capotosto/PS_Monitor/hardware/Isolated Multi-Rail Power Supply Monitor Arduino Shield Board/Outputs/STEP/CGS-PSM-12_Rev-A_bottom.png

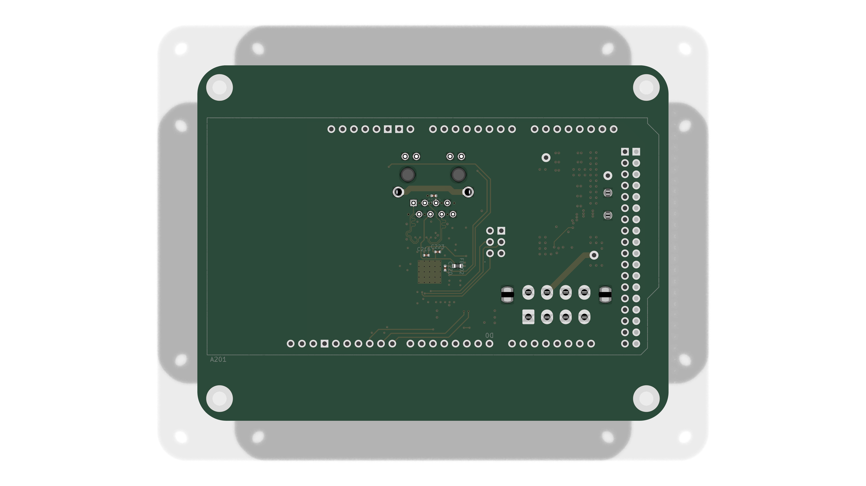
hardware/Isolated Multi-Rail Power Supply Monitor Arduino Shield Board/Outputs/STEP/CGS-PSM-12_Rev-A_bottom.png
