capotosto/PS_Monitor/hardware/Isolated Multi-Rail Power Supply Monitor Sensor Board/Outputs/STEP/CGS-PSM-02_Rev-A_bottom.png

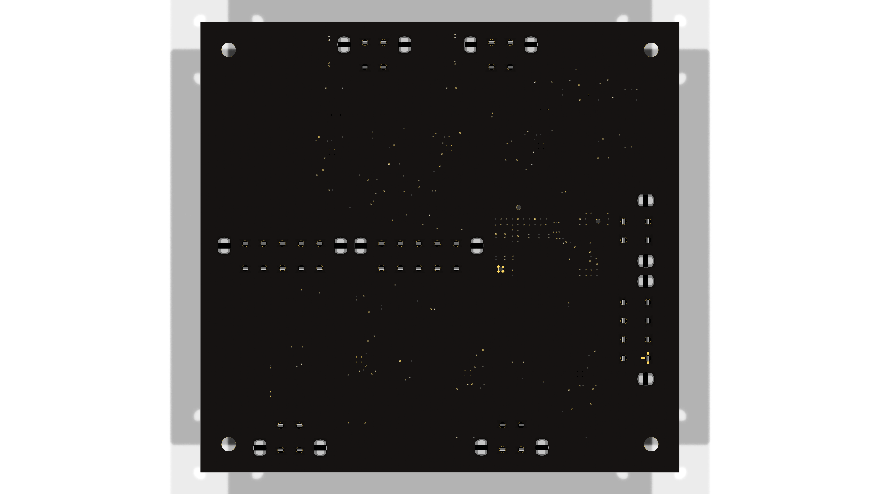
hardware/Isolated Multi-Rail Power Supply Monitor Sensor Board/Outputs/STEP/CGS-PSM-02_Rev-A_bottom.png
