capotosto/PS_Monitor/documentation/Pictures/Phoebus-SS-N5V-Test-3k3Load.png

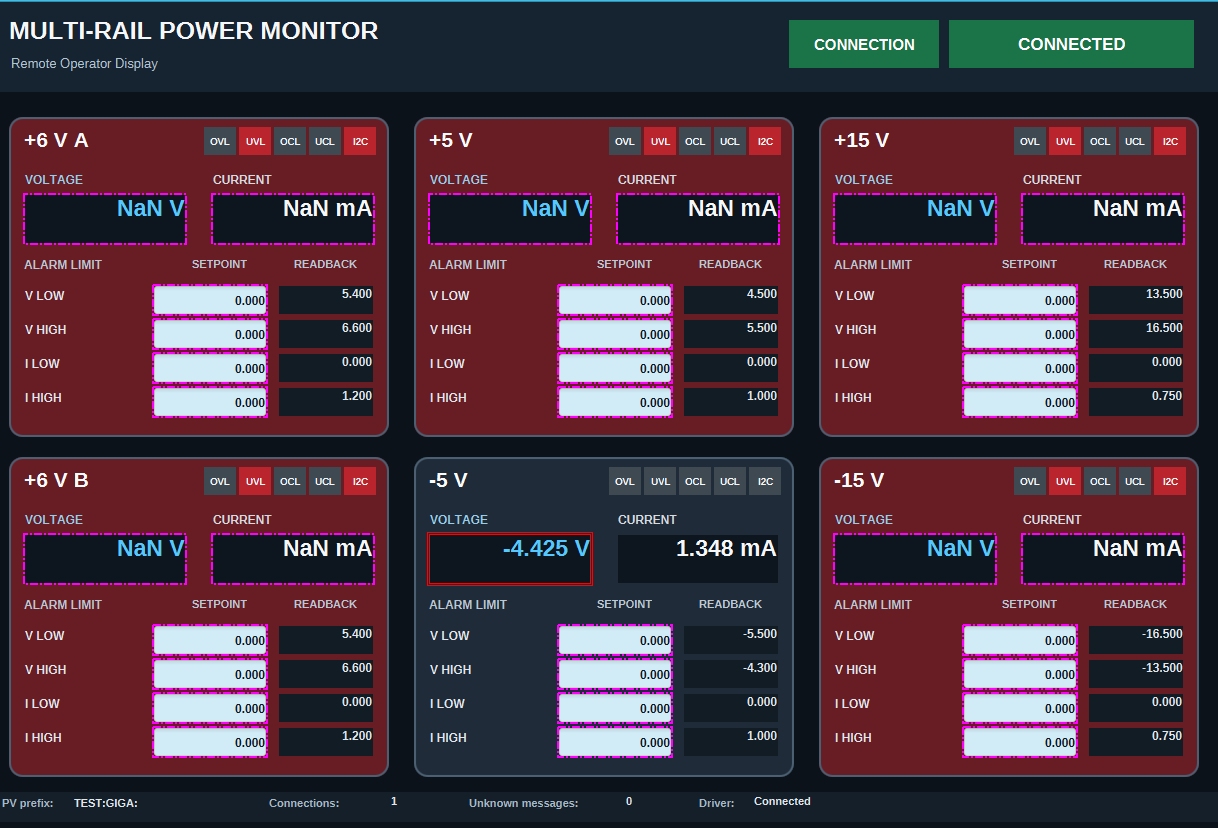
documentation/Pictures/Phoebus-SS-N5V-Test-3k3Load.png
