capotosto/PS_Monitor/documentation/Pictures/Phoebus-SS-N5V-Test-NoLoad-I2C-Fault.png

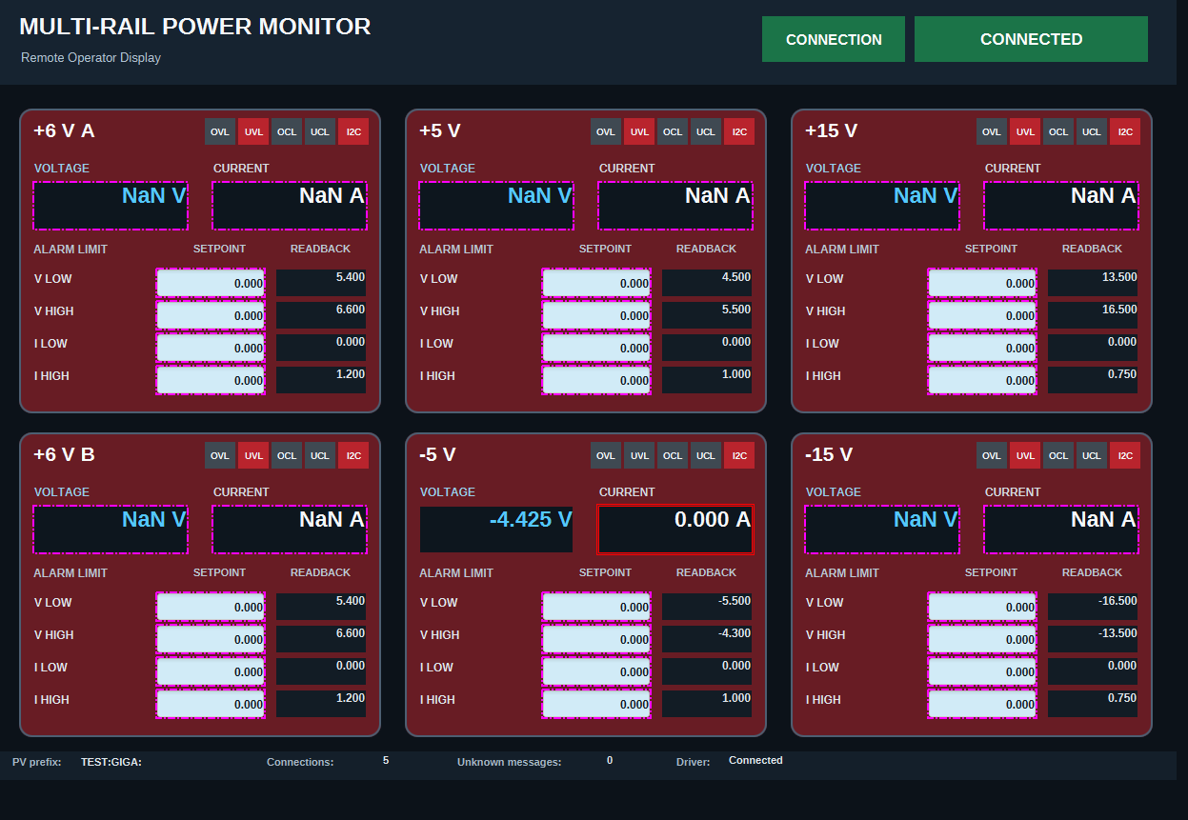
documentation/Pictures/Phoebus-SS-N5V-Test-NoLoad-I2C-Fault.png
