capotosto/PS_Monitor/documentation/Pictures/Phoebus-SS-N5V-Test-NoLoad.png

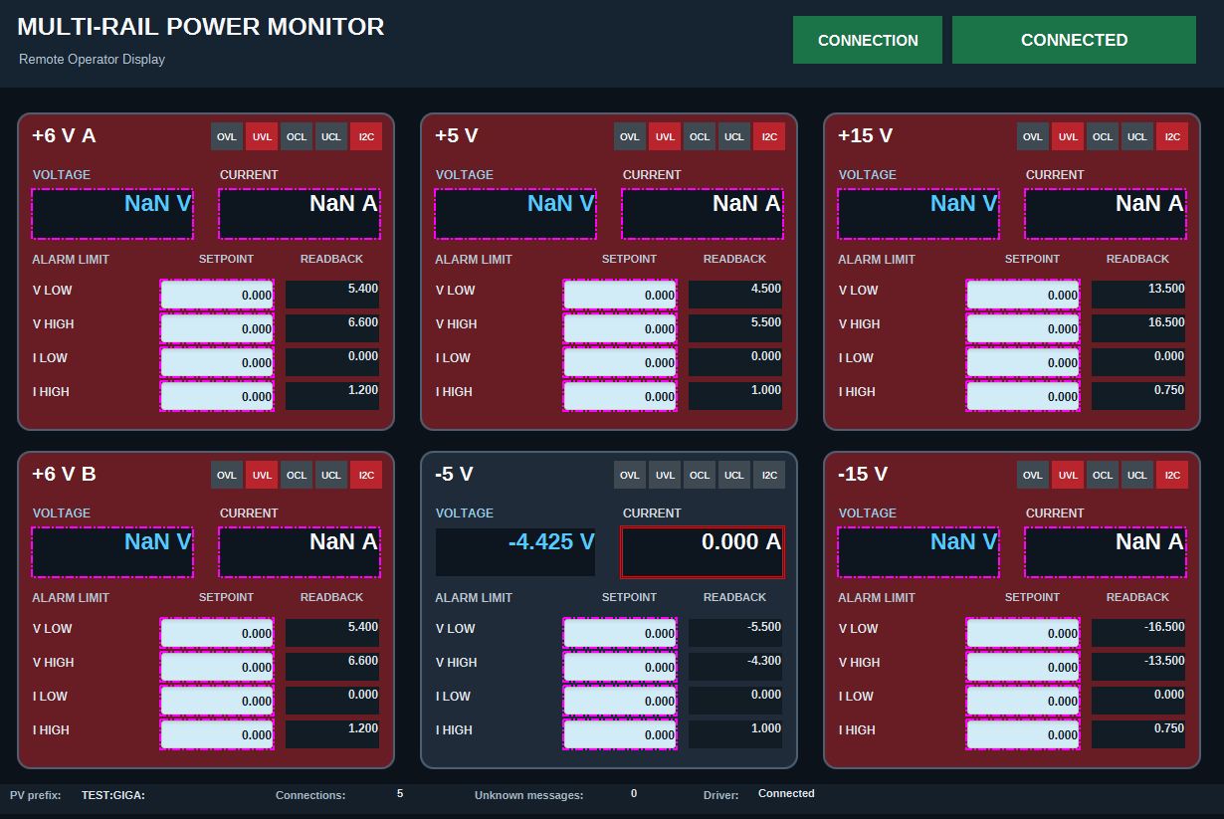
documentation/Pictures/Phoebus-SS-N5V-Test-NoLoad.png
