capotosto/PS_Monitor/documentation/Pictures/SimulationResults.png

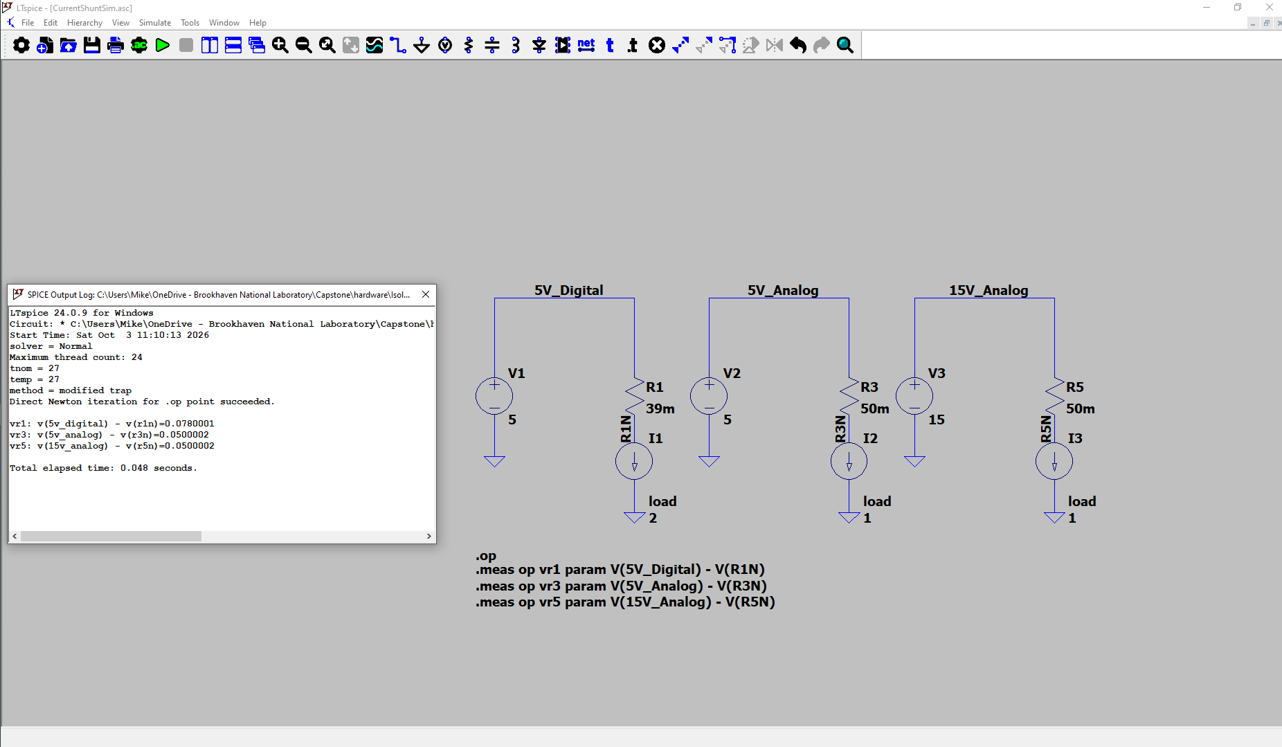
documentation/Pictures/SimulationResults.png
