capotosto/PS_Monitor/hardware/Isolated Multi-Rail Power Supply Monitor Sensor Board/Simulations/CurrentShuntSim.asc

I1: current; 2; load
I2: current; 1; load
I3: current; 1; load
R1: res; 39m; tol=0
R3: res; 50m; tol=0
R5: res; 50m; tol=0
V1: voltage; 5
V2: voltage; 5
V3: voltage; 15
Named nets: 0, 5V_Digital, 5V_Analog, 15V_Analog, R1N, R3N, R5N
.op
.meas op vr1 param V(5V_Digital) - V(R1N)
.meas op vr3 param V(5V_Analog) - V(R3N)
.meas op vr5 param V(15V_Analog) - V(R5N)
