capotosto/PS_Monitor/hardware/Isolated Multi-Rail Power Supply Monitor Arduino Shield Board/Isolated Multi-Rail Power Supply Monitor Arduino Shield Board.kicad_sch

## KiCad design hardware/Isolated Multi-Rail Power Supply Monitor Arduino Shield Board/Isolated Multi-Rail Power Supply Monitor Arduino Shield Board.kicad_sch (2026-09-21)

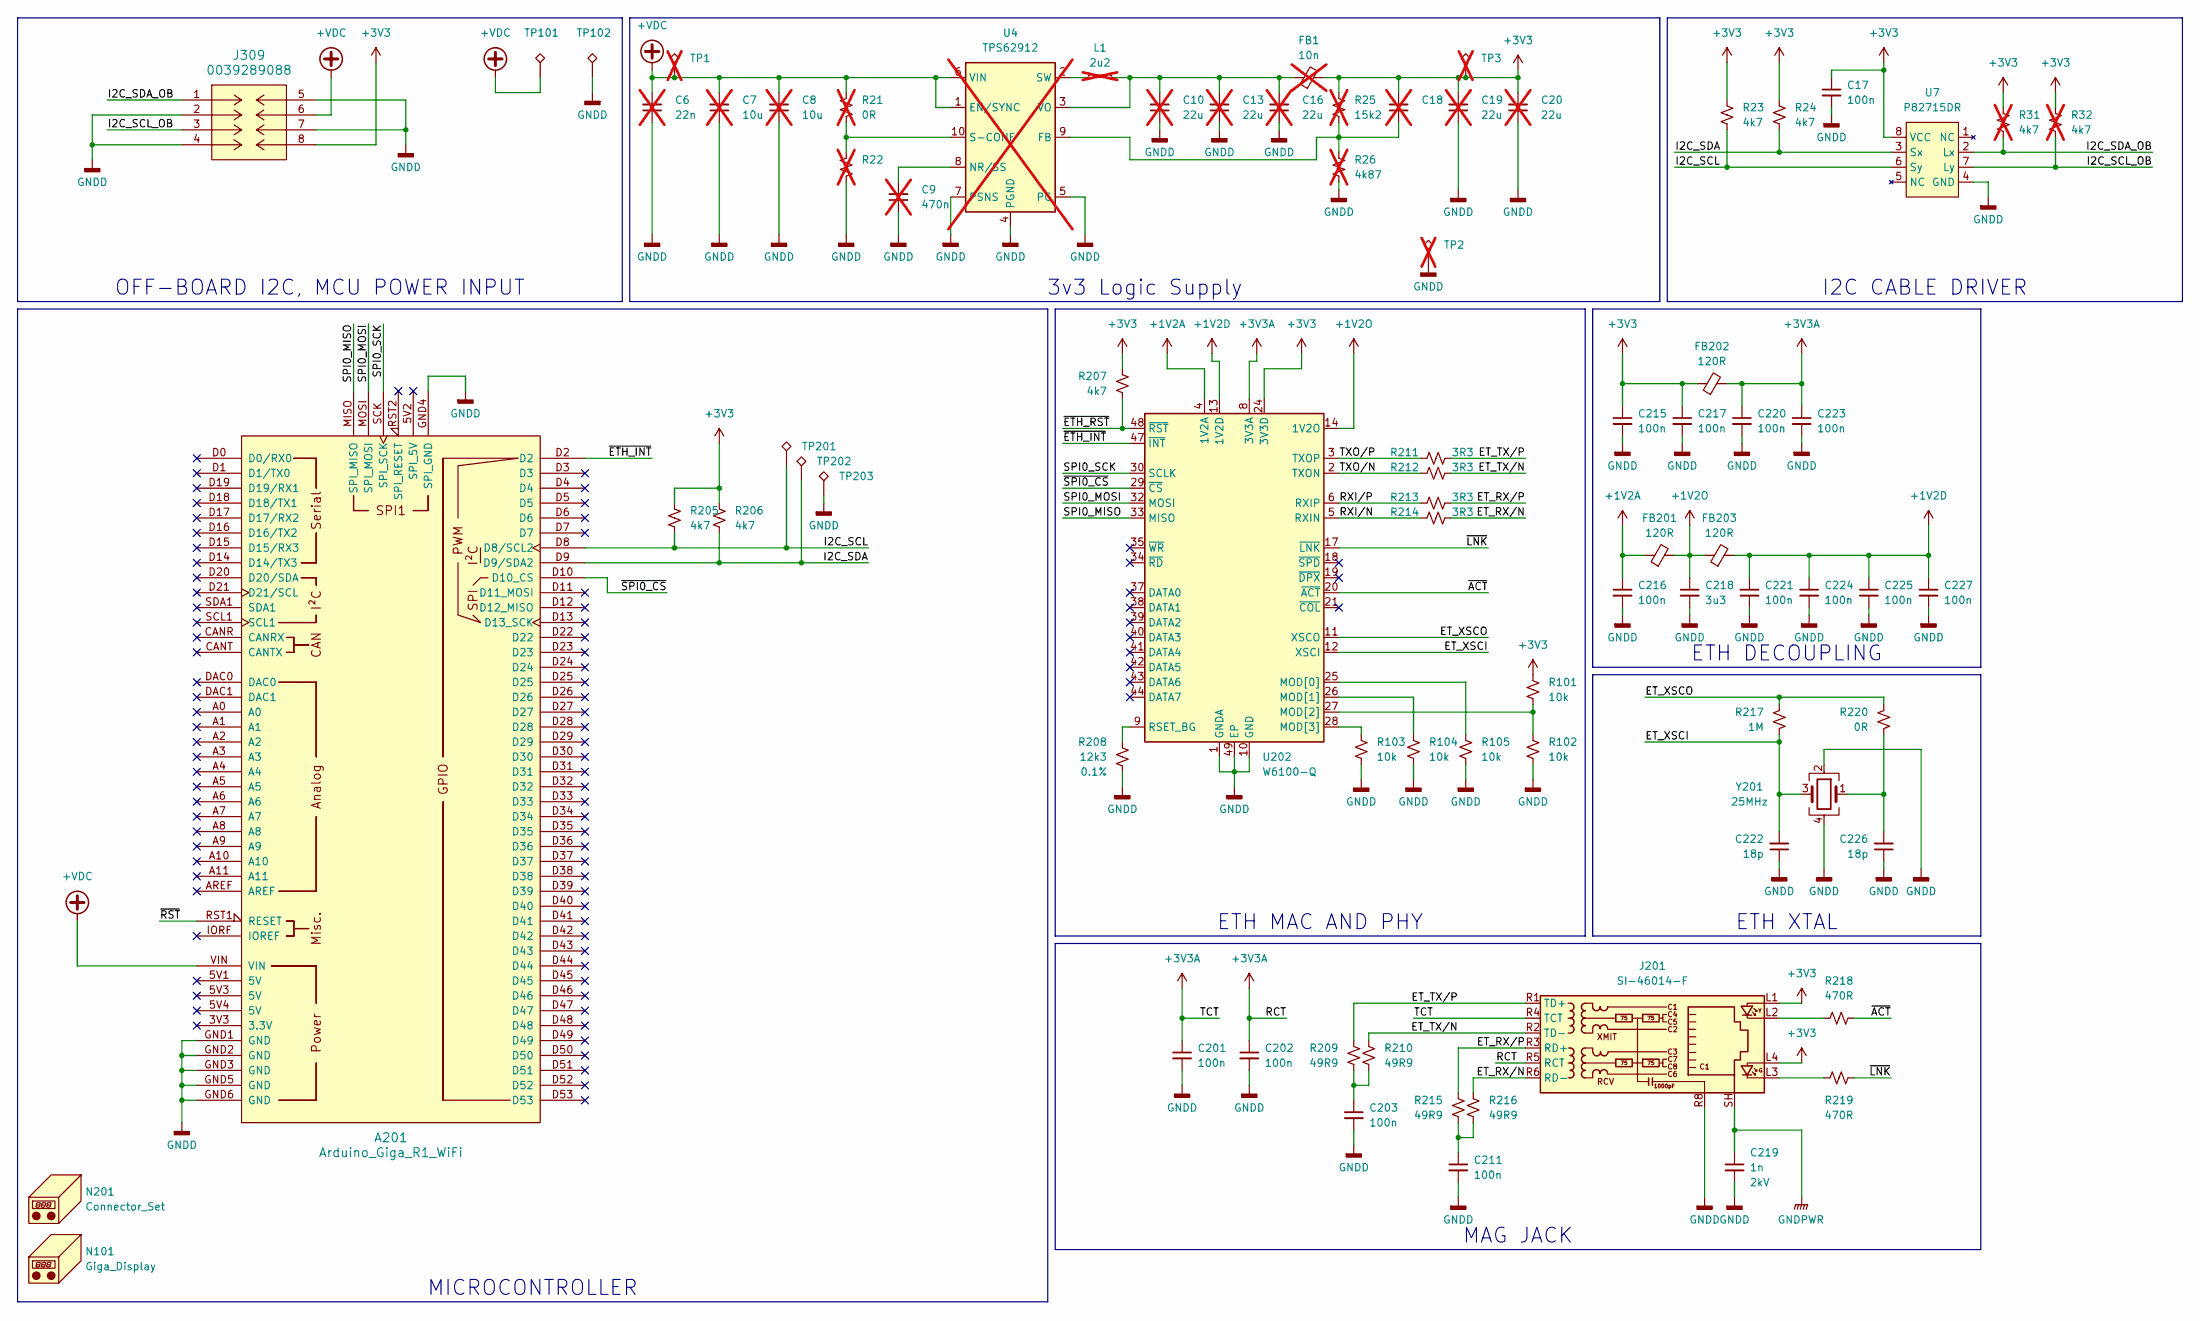
[picture p59: schematic Isolated Multi-Rail Power Supply Monitor Arduino Shield Board.kicad_sch]

Parts:
A201: Arduino_Giga_R1_WiFi; Arduino_Giga_R1_WiFi_Shield; MPN ABX00063
C6: 22n; C_0402_1005Metric; MPN GRM155R71H222KA01D; not fitted
C7, C8: 10u; C_0805_2012Metric; MPN C2012X7S1E106K125AC; not fitted
C9: 470n; C_0402_1005Metric; MPN C1005X5R1E474K050BB; not fitted
C10, C13, C16, C19, C20: 22u; C_0805_2012Metric; MPN GMC21X7S226M10NT; not fitted
C17, C201, C202, C203, C211, C215, C216, C217, C220, C221, C223, C224, C225, C227: 100n; C_0402_1005Metric; MPN GRM155R61H104KE14D
C18: C_0603_1608Metric; not fitted
C218: 3u3; C_0603_1608Metric; MPN GMC10X5R335K25NT
C219: 1n; C_1206_3216Metric; MPN 1206GC102KAT1A
C222, C226: 18p; C_0402_1005Metric; MPN GRM1555C1H180JA01D
FB1: 10n; L_0603_1608Metric; MPN BLE18PS080SN1D; not fitted
FB201, FB202, FB203: 120R; L_0603_1608Metric; MPN BBUP00160805121Y00
J201: SI-46014-F; BEL_SI-46014-F; MPN SI-46014-F
J309: 0039289088; Molex_Mini-Fit_Jr_5566-08A2_2x04_P4.20mm_Vertical; MPN 0039289088
L1: 2u2; 74438356022; MPN 74438356022; not fitted
N101: Giga_Display; MPN ASX00039
N201: Connector_Set; MPN 85
R21: 0R; R_0402_1005Metric; not fitted
R22: R_0402_1005Metric_Pad0.72x0.64mm_HandSolder; not fitted
R23, R24, R205, R206, R207: 4k7; R_0402_1005Metric; MPN CRCW04024K70FKED
R25: 15k2; R_0402_1005Metric; not fitted
R26: 4k87; R_0402_1005Metric; not fitted
R31, R32: 4k7; R_0402_1005Metric; MPN ERJ-2RKF4701X; not fitted
R101, R102, R103, R104, R105: 10k; R_0402_1005Metric; MPN ERJ-2RKF1002X
R208: 12k3; R_0402_1005Metric; Tolerance 0.1%; MPN RN73R1ETTP1232B25
R209, R210, R215, R216: 49R9; R_0402_1005Metric; MPN CRCW040249R9FKED
R211, R212, R213, R214: 3R3; R_0402_1005Metric; Tolerance 1%; MPN CRCW04023R30FKED
R217: 1M; R_0402_1005Metric; MPN CRCW04021M00FKED
R218, R219: 470R; R_0402_1005Metric; MPN ERJ-2RKF4700X
R220: 0R; R_0402_1005Metric; MPN CRCW04020000Z0ED
TP1, TP3: TestPoint_Alt; TestPoint_Keystone_5000-5004_Miniature; MPN 5000; not fitted
TP2: TestPoint_Alt; TestPoint_Keystone_5000-5004_Miniature; MPN 5001; not fitted
TP101: TestPoint_Alt; TestPoint_Keystone_5000-5004_Miniature; MPN 5000
TP102: TestPoint_Alt; TestPoint_Keystone_5000-5004_Miniature; MPN 5001
TP201, TP202, TP203: TestPoint_Alt; TestPoint_Keystone_5015_Micro_Mini; MPN 5015
U4: TPS62912; Texas_RPU0010A_VQFN-HR-10_2x2mm_P0.5mm; MPN TPS62912RPUR; not fitted
U7: P82715DR; SOIC-8_3.9x4.9mm_P1.27mm; MPN P82B715DR
U202: W6100-Q; QFN-48-1EP_7x7mm_P0.5mm_EP5.3x5.3mm_ThermalVias; MPN W6100Q
Y201: 25MHz; Crystal_SMD_3225-4Pin_3.2x2.5mm; MPN FL2500169

Connections:
+1V2A: C216.1, FB201.1, U202.4 (1V2A)
+1V2D: C221.1, C224.1, C225.1, C227.1, FB203.2, U202.13 (1V2D), U202.22 (1V2D), U202.31 (1V2D), U202.45 (1V2D)
+1V2O: C218.1, FB201.2, FB203.1, U202.14 (1V2O)
+3V3: C17.1, C18.2, C19.2, C20.2, C215.1, C217.1, FB1.2, FB202.1, J201.L1, J201.L4, J309.8, R23.2, R24.2, R25.1, R31.2, R32.2, R101.1, R205.2, R206.2, R207.2, TP3.1, U7.8 (VCC), U202.24 (3V3D), U202.36 (3V3D)
+3V3A: C201.1, C202.1, C220.1, C223.1, FB202.2, J201.R4 (TCT), J201.R5 (RCT), U202.8 (3V3A), U202.15 (3V3A)
+VDC: A201.VIN, C6.2, C7.2, C8.2, J309.6, R21.1, TP1.1, TP101.1, U4.1 (EN/SYNC), U4.6 (VIN)
ET_RX/N: J201.R6 (RD-), R214.1, R216.2
ET_RX/P: J201.R3 (RD+), R213.1, R215.2
ET_TX/N: J201.R2 (TD-), R210.2, R212.1
ET_TX/P: J201.R1 (TD+), R209.2, R211.1
ET_XSCI: C222.2, R217.1, U202.12 (XSCI), Y201.3
ET_XSCO: R217.2, R220.2, U202.11 (XSCO)
GNDD: A201.GND1 (GND), A201.GND2 (GND), A201.GND3 (GND), A201.GND4 (SPI_GND), A201.GND5 (GND), A201.GND6 (GND), C6.1, C7.1, C8.1, C9.1, C10.1, C13.1, C16.1, C17.2, C19.1, C20.1, C201.2, C202.2, C203.2, C211.2, C215.2, C216.2, C217.2, C218.2, C219.2, C220.2, C221.2, C222.1, C223.2, C224.2, C225.2, C226.1, C227.2, J201.R8, J309.2, J309.4, J309.5, J309.7, R22.2, R26.2, R102.2, R103.2, R104.2, R105.2, R208.1, TP2.1, TP102.1, TP203.1, U4.4 (PGND), U4.5 (PG), U4.7 (PSNS), U7.4 (GND), U202.1 (GNDA), U202.7 (GNDA), U202.10 (GND), U202.16 (GNDA), U202.23 (GND), U202.46 (GND), U202.49 (EP), Y201.2, Y201.4
GNDPWR: C219.1, J201.SH
I2C_SCL: A201.D8 (D8/SCL2), R23.1, R205.1, TP201.1, U7.6 (Sy)
I2C_SCL_OB: J309.3, R32.1, U7.7 (Ly)
I2C_SDA: A201.D9 (D9/SDA2), R24.1, R206.1, TP202.1, U7.3 (Sx)
I2C_SDA_OB: J309.1, R31.1, U7.2 (Lx)
unnamed: C9.2, U4.8 (NR/SS)
unnamed: C10.2, C13.2, C16.2, FB1.1, L1.2, U4.3 (VO)
unnamed: C18.1, R25.2, R26.1, U4.9 (FB)
unnamed: C203.1, R209.1, R210.1
unnamed: C211.1, R215.1, R216.1
unnamed: C226.2, R220.1, Y201.1
unnamed: J201.L2, R218.2
unnamed: J201.L3, R219.2
unnamed: L1.1, U4.2 (SW)
unnamed: R21.2, R22.1, U4.10 (S-CONF)
unnamed: R101.2, R102.1, U202.27 (MOD[2])
unnamed: R103.1, U202.28 (MOD[3])
unnamed: R104.1, U202.26 (MOD[1])
unnamed: R105.1, U202.25 (MOD[0])
unnamed: R208.2, U202.9 (RSET_BG)
RXI/N: R214.2, U202.5 (RXIN)
RXI/P: R213.2, U202.6 (RXIP)
SPI0_MISO: A201.MISO (SPI_MISO), U202.33 (MISO)
SPI0_MOSI: A201.MOSI (SPI_MOSI), U202.32 (MOSI)
SPI0_SCK: A201.SCK (SPI_SCK), U202.30 (SCLK)
TXO/N: R212.2, U202.2 (TXON)
TXO/P: R211.2, U202.3 (TXOP)
~ACT: R218.1, U202.20 (~ACT)
~ETH_INT: A201.D2, U202.47 (~INT)
~ETH_RST: R207.1, U202.48 (~RST)
~LNK: R219.1, U202.17 (~LNK)
~RST: A201.RST1 (RESET)
~SPI0_CS: A201.D10 (D10_CS), U202.29 (~CS)

Notes on the sheet:
ETH DECOUPLING
MICROCONTROLLER
MAG JACK
OFF-BOARD I2C, MCU POWER INPUT
3v3 Logic Supply
ETH XTAL
ETH MAC AND PHY
I2C CABLE DRIVER
