capotosto/PS_Monitor/hardware/Isolated Multi-Rail Power Supply Monitor Sensor Board/Isolated Multi-Rail Power Supply Monitor Sensor Board.kicad_sch

## KiCad design hardware/Isolated Multi-Rail Power Supply Monitor Sensor Board/Isolated Multi-Rail Power Supply Monitor Sensor Board.kicad_sch (2026-10-03)

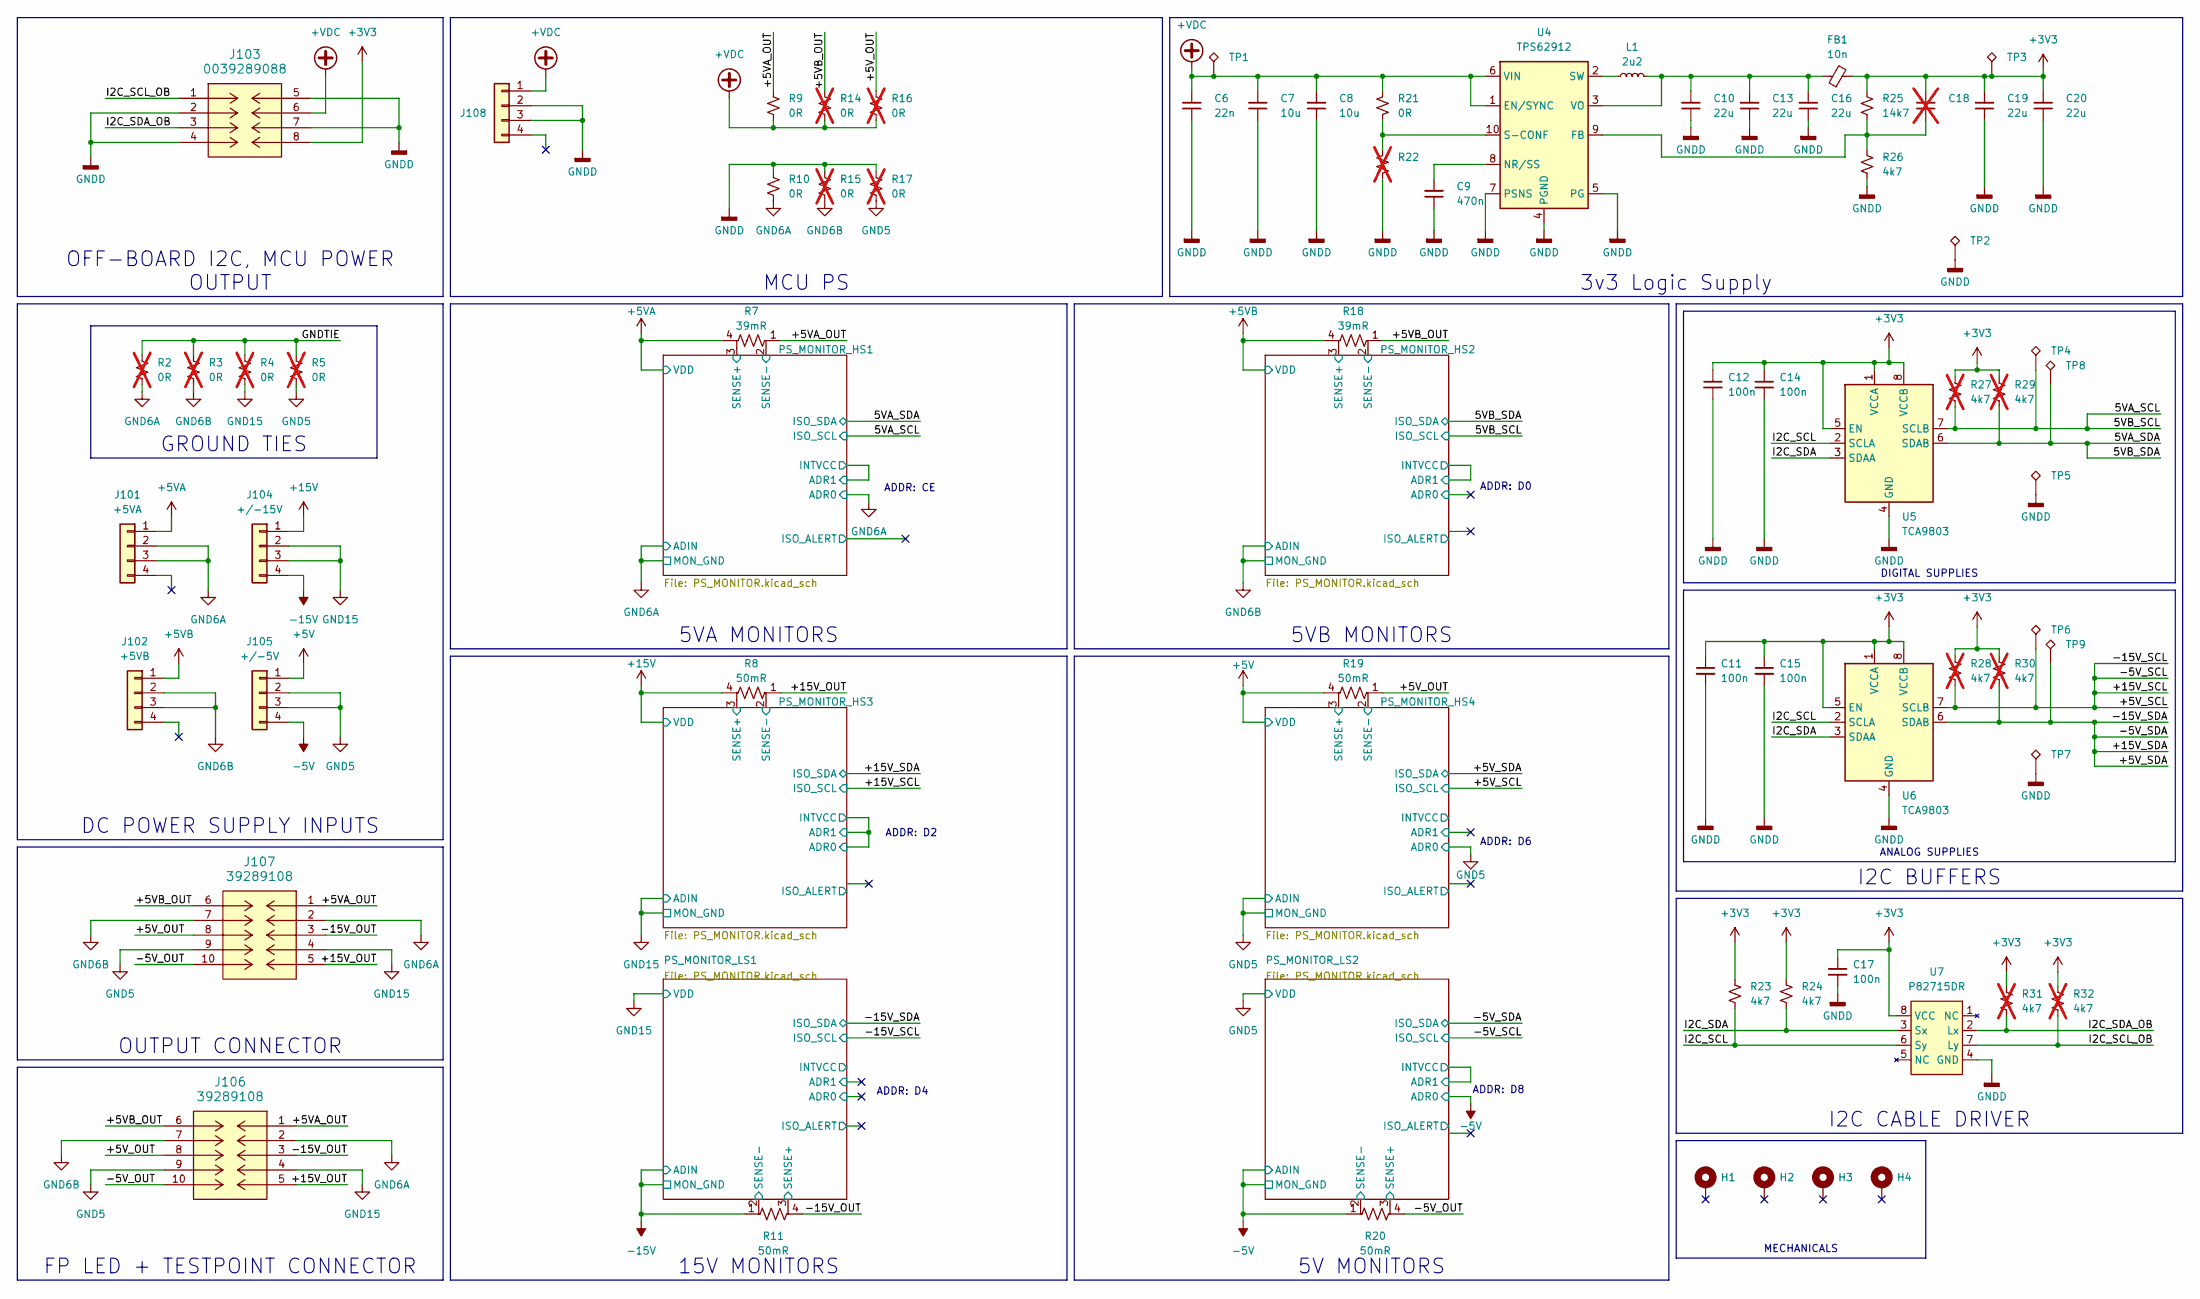
[picture p60: schematic Isolated Multi-Rail Power Supply Monitor Sensor Board.kicad_sch]

Parts:
C6: 22n; C_0402_1005Metric; MPN GRM155R71H222KA01D
C7, C8: 10u; C_0805_2012Metric; MPN C2012X7S1E106K125AC
C9: 470n; C_0402_1005Metric; MPN C1005X5R1E474K050BB
C10, C13, C16, C19, C20: 22u; C_0805_2012Metric; MPN GMC21X7S226M10NT
C11, C12, C14, C15, C17: 100n; C_0402_1005Metric; MPN GRM155R61H104KE14D
C18: C_0603_1608Metric; not fitted
FB1: 10n; L_0603_1608Metric; MPN BLE18PS080SN1D
H1, H2, H3, H4: MountingHole_Pad; MountingHole_3.2mm_M3_DIN965_Pad
J101: +5VA; Molex_Mini-Fit_Jr_5566-04A2_2x02_P4.20mm_Vertical; MPN 0039299049
J102: +5VB; Molex_Mini-Fit_Jr_5566-04A2_2x02_P4.20mm_Vertical; MPN 0039299049
J103: 0039289088; Molex_Mini-Fit_Jr_5566-08A2_2x04_P4.20mm_Vertical; MPN 0039289088
J104: +/-15V; Molex_Mini-Fit_Jr_5566-04A2_2x02_P4.20mm_Vertical; MPN 0039299049
J105: +/-5V; Molex_Mini-Fit_Jr_5566-04A2_2x02_P4.20mm_Vertical; MPN 0039299049
J106, J107: 39289108; Molex_Mini-Fit_Jr_5566-10A2_2x05_P4.20mm_Vertical; MPN 0039289108
J108: Conn_01x04; Molex_Mini-Fit_Jr_5566-04A2_2x02_P4.20mm_Vertical; MPN 0039299049
L1: 2u2; 74438356022; MPN 74438356022
R2, R3, R4, R5, R14, R15, R16, R17: 0R; R_1206_3216Metric; Tolerance JUMPER; MPN 5108; not fitted
R7, R18: 39mR; R_Shunt_Ohmite_LVK20; MPN LVK20R039FER
R8, R11, R19, R20: 50mR; R_Shunt_Ohmite_LVK20; MPN LVK20R050FER
R9, R10: 0R; R_1206_3216Metric; Tolerance JUMPER; MPN 5108
R21: 0R; R_0402_1005Metric; MPN CRCW04020000Z0ED
R22: R_0402_1005Metric; not fitted
R23, R24: 4k7; R_0402_1005Metric; MPN CRCW04024K70FKED
R25: 14k7; R_0402_1005Metric; MPN ERA-2APB1472X
R26: 4k7; R_0402_1005Metric; MPN ERA-2ARB472X
R27, R28, R29, R30, R31, R32: 4k7; R_0402_1005Metric; MPN CRCW04024K70FKED; not fitted
TP1, TP3: 5000; TestPoint_Keystone_5000-5004_Miniature; MPN 5000
TP2: 5001; TestPoint_Keystone_5000-5004_Miniature; MPN 5001
TP4, TP5, TP6, TP7, TP8, TP9: 5015; TestPoint_Keystone_5015_Micro_Mini; MPN 5015
U4: TPS62912; Texas_RPU0010A_VQFN-HR-10_2x2mm_P0.5mm; MPN TPS62912RPUR
U5, U6: TCA9803; VSSOP-8_3x3mm_P0.65mm; MPN TCA9803DGKR
U7: P82715DR; SOIC-8_3.9x4.9mm_P1.27mm; MPN P82B715DR

Connections:
5VA_SCL: R27.1, TP4.1, U5.7 (SCLB)
5VA_SDA: R29.1, TP8.1, U5.6 (SDAB)
+3V3: C11.1, C12.1, C14.1, C15.1, C17.1, C18.2, C19.2, C20.2, FB1.2, J103.8, R23.2, R24.2, R25.1, R27.2, R28.2, R29.2, R30.2, R31.2, R32.2, TP3.1, U5.1 (VCCA), U5.5 (EN), U5.8 (VCCB), U6.1 (VCCA), U6.5 (EN), U6.8 (VCCB), U7.8 (VCC)
+5V: J105.1, R19.4
+5VA: J101.1, R7.4
+5VA_OUT: J106.1, J107.1, R7.1, R9.1
+5VB: J102.1, R18.4
+5VB_OUT: J106.6, J107.6, R14.1, R18.1
+5V_OUT: J106.8, J107.8, R16.1, R19.1
+15V: J104.1, R8.4
+15V_OUT: J106.5, J107.5, R8.1
+15V_SCL: R28.1, TP6.1, U6.7 (SCLB)
+15V_SDA: R30.1, TP9.1, U6.6 (SDAB)
+VDC: C6.2, C7.2, C8.2, J103.6, J108.1, R9.2, R14.2, R16.2, R21.1, TP1.1, U4.1 (EN/SYNC), U4.6 (VIN)
-5V: J105.4, R20.1
-5V_OUT: J106.10, J107.10, R20.4
-15V: J104.4, R11.1
-15V_OUT: J106.3, J107.3, R11.4
GND5: J105.2, J105.3, J106.9, J107.9, R5.2, R17.2
GND6A: J101.2, J101.3, J106.2, J107.2, R2.2, R10.2
GND6B: J102.2, J102.3, J106.7, J107.7, R3.2, R15.2
GND15: J104.2, J104.3, J106.4, J107.4, R4.2
GNDD: C6.1, C7.1, C8.1, C9.1, C10.1, C11.2, C12.2, C13.1, C14.2, C15.2, C16.1, C17.2, C19.1, C20.1, J103.2, J103.4, J103.5, J103.7, J108.2, J108.3, R10.1, R15.1, R17.1, R22.2, R26.2, TP2.1, TP5.1, TP7.1, U4.4 (PGND), U4.5 (PG), U4.7 (PSNS), U5.4 (GND), U6.4 (GND), U7.4 (GND)
GNDTIE: R2.1, R3.1, R4.1, R5.1
I2C_SCL: R23.1, U5.2 (SCLA), U6.2 (SCLA), U7.6 (Sy)
I2C_SCL_OB: J103.1, R32.1, U7.7 (Ly)
I2C_SDA: R24.1, U5.3 (SDAA), U6.3 (SDAA), U7.3 (Sx)
I2C_SDA_OB: J103.3, R31.1, U7.2 (Lx)
unnamed: C9.2, U4.8 (NR/SS)
unnamed: C10.2, C13.2, C16.2, FB1.1, L1.2, U4.3 (VO)
unnamed: C18.1, R25.2, R26.1, U4.9 (FB)
unnamed: L1.1, U4.2 (SW)
unnamed: R21.2, R22.1, U4.10 (S-CONF)
SENSE+: R7.3, R8.3, R11.3, R18.3, R19.3, R20.3
SENSE-: R7.2, R8.2, R11.2, R18.2, R19.2, R20.2

Notes on the sheet:
ADDR: D0
ADDR: D6
ADDR: D2
ADDR: D4
ADDR: D8
ADDR: CE
I2C BUFFERS
ANALOG SUPPLIES
5V MONITORS
5VA MONITORS
OFF-BOARD I2C, MCU POWER OUTPUT
3v3 Logic Supply
GROUND TIES
I2C CABLE DRIVER
5VB MONITORS
15V MONITORS
MECHANICALS
FP LED + TESTPOINT CONNECTOR
OUTPUT CONNECTOR
MCU PS
DC POWER SUPPLY INPUTS
DIGITAL SUPPLIES
