capotosto/PS_Monitor/hardware/Isolated Multi-Rail Power Supply Monitor Sensor Board/PS_MONITOR.kicad_sch

## KiCad design hardware/Isolated Multi-Rail Power Supply Monitor Sensor Board/PS_MONITOR.kicad_sch (2026-09-11)

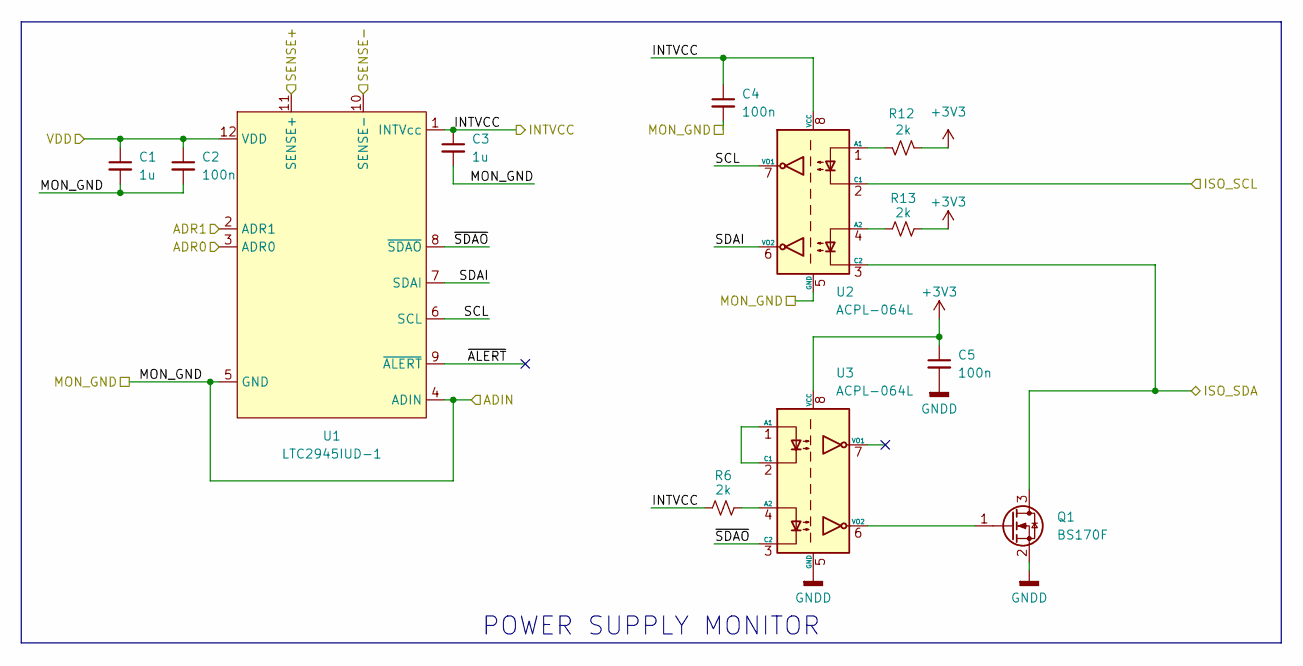
[picture p61: schematic PS_MONITOR.kicad_sch]

Parts:
C1, C3: 1u; C_0603_1608Metric; MPN CL10A105KB8NNNC
C2, C4, C5: 100n; C_0402_1005Metric; MPN GRM155R61H104KE14D
Q1: BS170F; SOT-416; MPN NTA7002NT1G
R6, R12, R13: 2k; R_0402_1005Metric; MPN ERJ-2RKF2001X
U1: LTC2945IUD-1; QFN-12-1EP_3x3mm_P0.5mm_EP1.65x1.65mm_ThermalVias; MPN LTC2945IUD#TRPBF
U2, U3: ACPL-064L; SOIC-8_3.9x4.9mm_P1.27mm; MPN ACPL-064L-500E

Connections:
+3V3: C5.1, R12.1, R13.2
ADIN: C1.2, C2.2, C3.2, C4.2, U1.4 (ADIN), U1.5 (GND), U1.13 (GND)
ADR0: U1.3 (ADR0)
ADR1: U1.2 (ADR1)
GNDD: C5.2, Q1.2 (S)
INTVCC: C3.1, C4.1, R6.1, U1.1 (INTVcc)
ISO_SDA: Q1.3 (D)
unnamed: U3.1 (A1), U3.2 (C1)
SCL: U1.6 (SCL)
SDAI: U1.7 (SDAI)
SENSE+: U1.11 (SENSE+)
SENSE-: U1.10 (SENSE-)
VDD: C1.1, C2.1, U1.12 (VDD)
~ALERT: U1.9 (~ALERT)
~SDAO: U1.8 (~SDAO)

Notes on the sheet:
POWER SUPPLY MONITOR
